Patave/AutodiDICE/IMG_3947.jpg

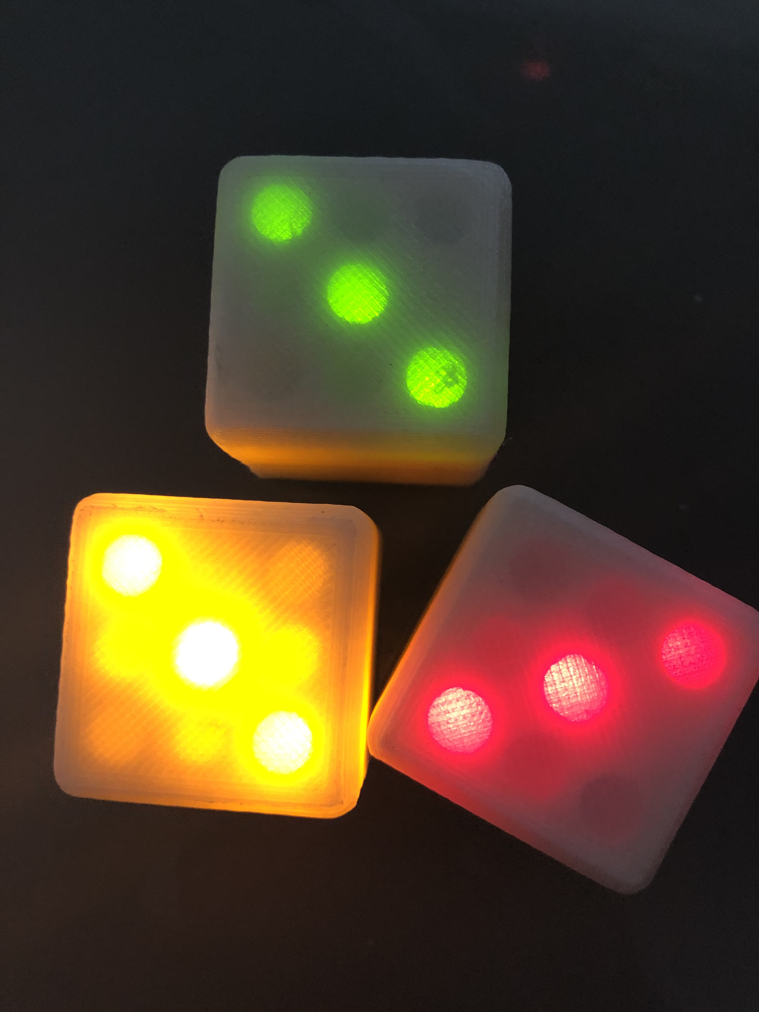
IMG_3947.jpg
