Patave/AutodiDICE/IMG_3948.jpg

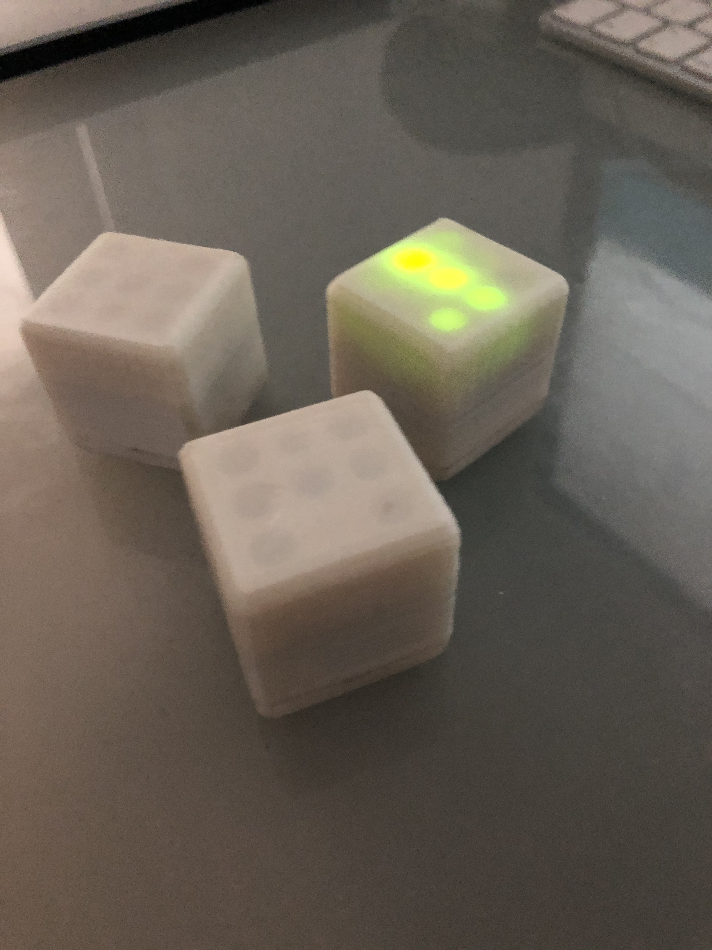
IMG_3948.jpg
