Patave/AutodiDICE/IMG_3949.jpg

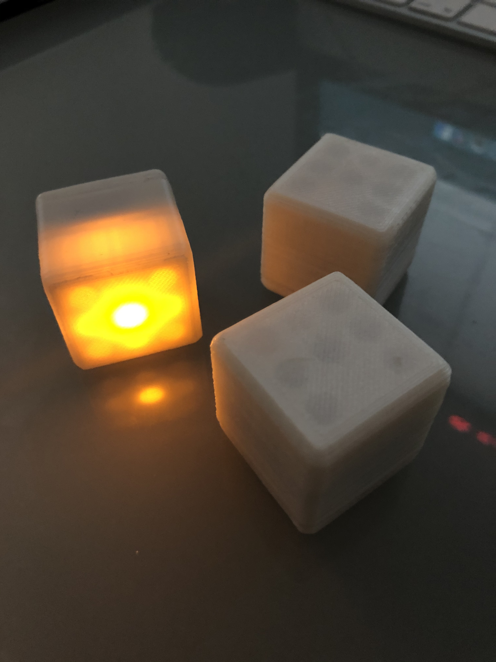
IMG_3949.jpg
