Patave/AutodiDICE/IMG_4037.jpeg

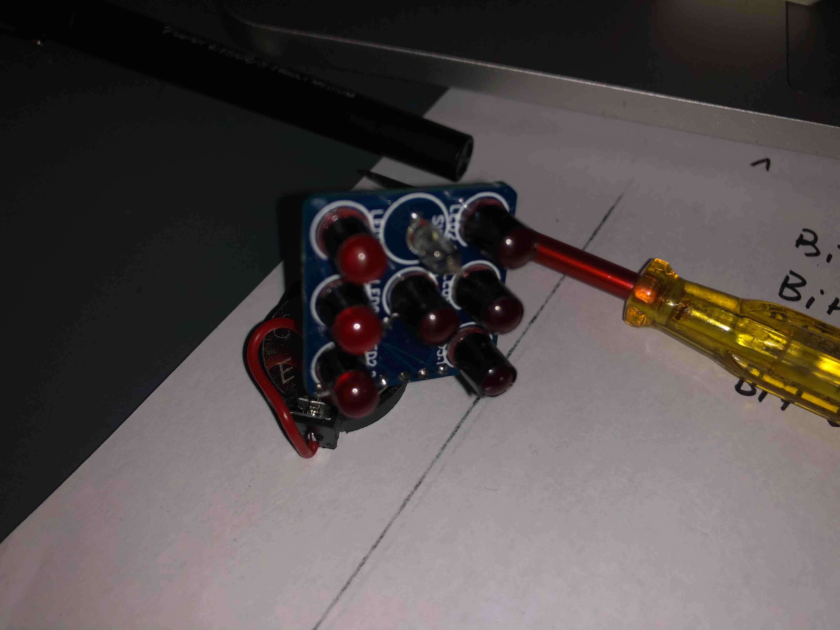
IMG_4037.jpeg
