Patave/AutodiDICE/IMG_4038.jpeg

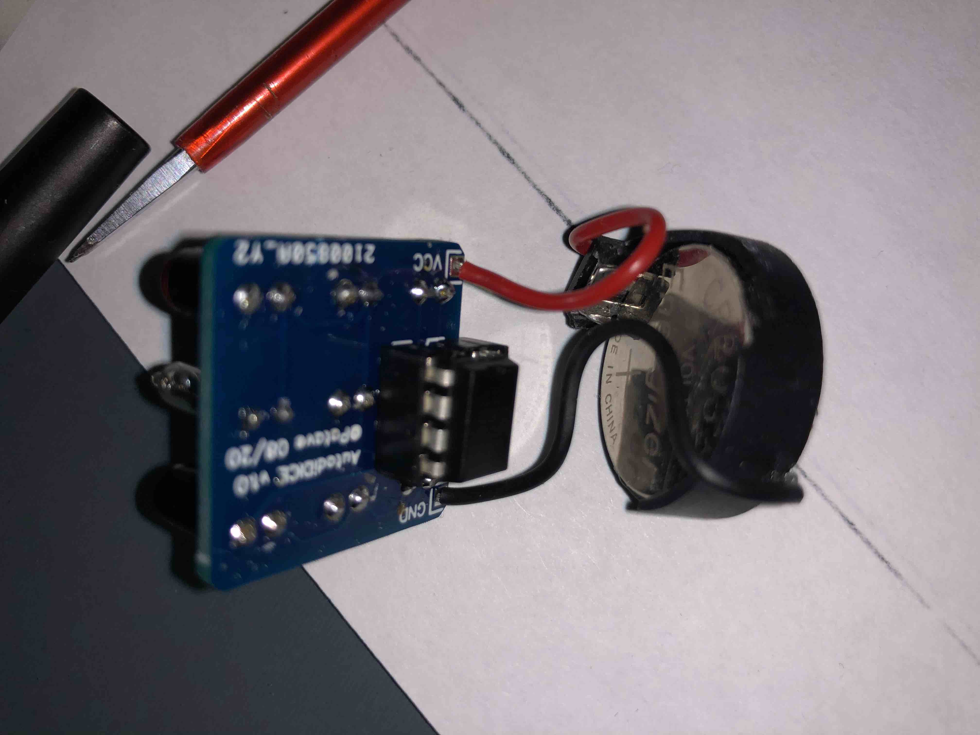
IMG_4038.jpeg
