Patave/AutodiDICE/IMG_4040.jpeg

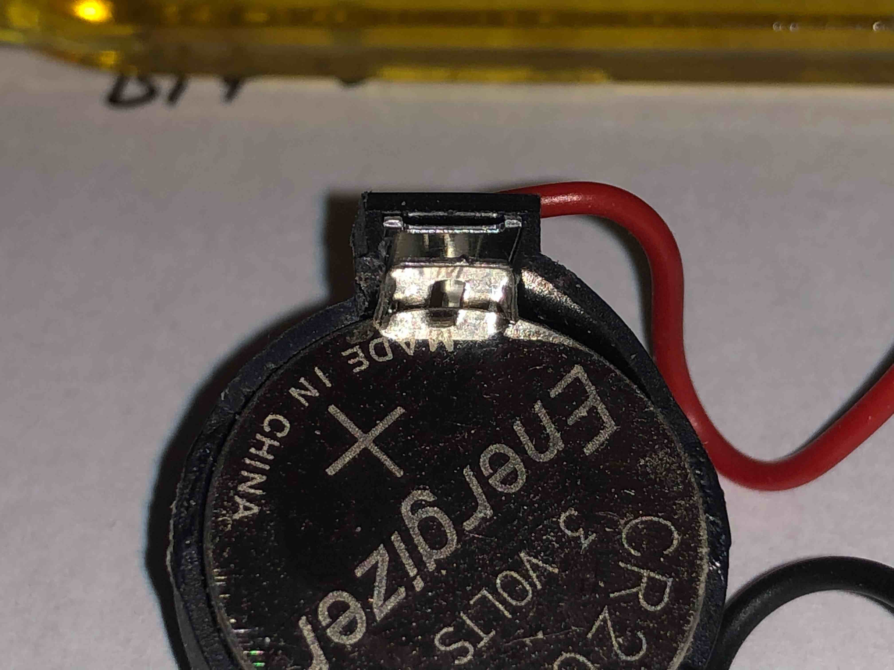
IMG_4040.jpeg
