Patave/AutodiDICE/IMG_4041.jpeg

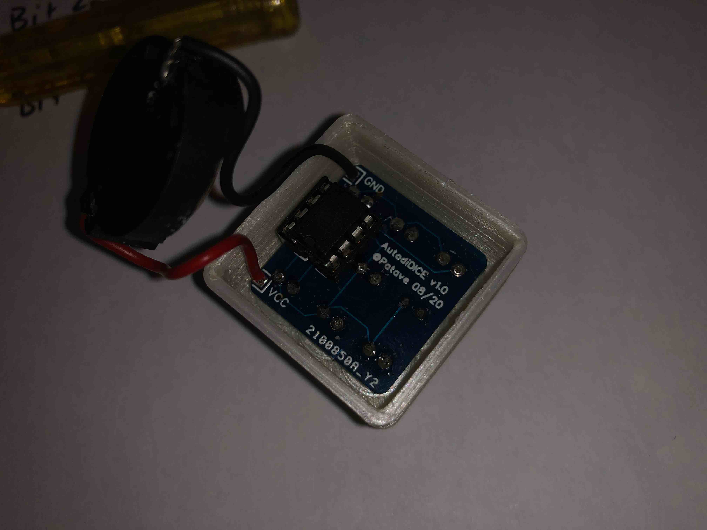
IMG_4041.jpeg
