Patave/AutodiDICE/IMG_4042.jpeg

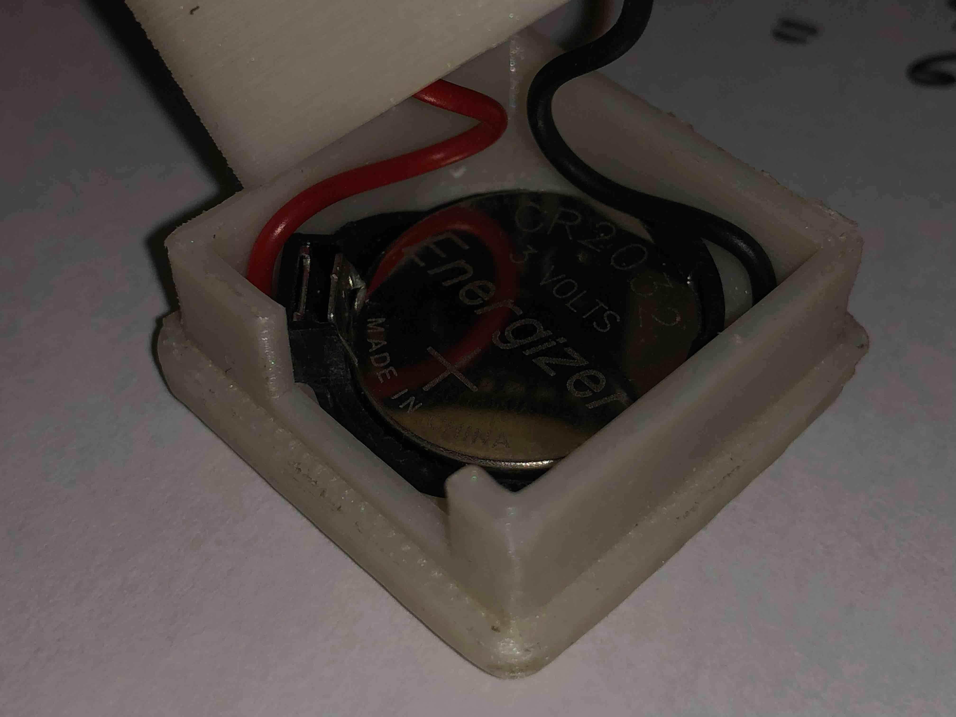
IMG_4042.jpeg
